maccody/KanaChord/software/kana.h

// kana.h - Hiragana and Katakana Unicode characters.
/**
This file is part of KanaChord Keyboard.
 Copyright (C) 2024 Mac A. Cody

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
 You should have received a copy of the GNU General Public License
 along with this program.  If not, see <http://www.gnu.org/licenses/>.
**/

// Hiragana base table.
//    a       i       u       e       o       n
const uint16_t hiraBase[10][6] =
  {{0x3042, 0x3044, 0x3046, 0x3048, 0x304a, 0x3093},  // vowel
   {0x304b, 0x304d, 0x304f, 0x3051, 0x3053, 0x0000},  // k
   {0x3055, 0x3057, 0x3059, 0x305b, 0x305d, 0x0000},  // s
   {0x305f, 0x3061, 0x3064, 0x3066, 0x3068, 0x0000},  // t
   {0x306a, 0x306b, 0x306c, 0x306d, 0x306e, 0x0000},  // n
   {0x306f, 0x3072, 0x3075, 0x3078, 0x307b, 0x0000},  // h
   {0x307e, 0x307f, 0x3080, 0x3081, 0x3082, 0x0000},  // m
   {0x3084, 0x0000, 0x3086, 0x0000, 0x3088, 0x0000},  // y
   {0x3089, 0x308a, 0x308b, 0x308c, 0x308d, 0x0000},  // r
   {0x308f, 0x0000, 0x0000, 0x0000, 0x3092, 0x0000}}; // w
//    a       i       u       e       o       n

// Hiragana Ten-Ten table.
//    a       i       u       e       o       n
const uint16_t hiraTenTen[10][6] =
  {{0x0000, 0x0000, 0x3094, 0x0000, 0x0000, 0x0000},  // vowel
   {0x304c, 0x304e, 0x3050, 0x3052, 0x3054, 0x0000},  // k
   {0x3056, 0x3058, 0x305a, 0x305c, 0x305e, 0x0000},  // s
   {0x3060, 0x3062, 0x3065, 0x3067, 0x3069, 0x0000},  // t
   {0x0000, 0x0000, 0x0000, 0x0000, 0x0000, 0x0000},  // n
   {0x3070, 0x3073, 0x3076, 0x3079, 0x307c, 0x0000},  // h
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

const uint16_t specialKataTen [2][6] =
  {{0x30fe, 0x3034, 0x0000, 0x0000, 0x0000, 0x0000},
   {0x0000, 0x0000, 0x0000, 0x0000, 0x0000, 0x0000}};

const uint16_t specialKataChi [2][6] =
  {{0x0000, 0x3035, 0x30fb, 0x3001, 0xff1f, 0x2026},
   {0x300e, 0x300f, 0x3008, 0x3009, 0x203b, 0x0000}};
